zjuwangrui/25GAuto-Circuit-Modelling/resources/3.AD9910模块-SINC波点频输出代码/AD9910-STM32-DDS驱动板-V0.6/HARDWARE/ad9910/AD9910V1.C

/**********************************************************
                       康威电子

功能：stm32f103rct6控制
接口：按键接口请参照AD9910.H
时间：
版本：0.6
作者：康威电子
其他：

更多电子需求，请到淘宝店，康威电子竭诚为您服务 ^_^
https://kvdz.taobao.com/
**********************************************************/

#include "stm32f10x.h"
#include "AD9910.h"
#include "delay.h"
#include "sys.h"


/////三角波 波形数据，1024个点，14DAC值，最大16383
const u32 RAM_TRIG_WAVE[]=																																														
{
0,31,63,95,127,159,191,223,255,287,319,351,383,415,447,479,511,543,575,607,639,671,703,735,767,799,831,863,895,927,959,991,1023,1055,1087,1119,1151,1183,1215,1247,1279,1311,1343,1375,1407,1439,1471,1503,1535,1567,1599,1631,1663,1695,1727,1759,1791,1823,1855,1887,1919,1951,1983,2015,2047,2079,2111,2143,2175,2207,2239,2271,2303,2335,2367,2399,2431,2463,2495,2527,2559,2591,2623,2655,2687,2719,2751,2783,2815,2847,2879,2911,2943,2975,3007,3039,3071,3103,3135,3167,3199,3231,3263,3295,3327,3359,3391,3423,3455,3487,3519,3551,3583,3615,3647,3679,3711,3743,3775,3807,3839,3871,3903,3935,3967,3999,4031,4063,4095,4127,4159,4191,4223,4255,4287,4319,4351,4383,4415,4447,4479,4511,4543,4575,4607,4639,4671,4703,4735,4767,4799,4831,4863,4895,4927,4959,4991,5023,5055,5087,5119,5151,5183,5215,5247,5279,5311,5343,5375,5407,5439,5471,5503,5535,5567,5599,5631,5663,5695,5727,5759,5791,5823,5855,5887,5919,5951,5983,6015,6047,6079,6111,6143,6175,6207,6239,6271,6303,6335,6367,6399,6431,6463,6495,6527,6559,6591,6623,6655,6687,6719,6751,6783,6815,6847,6879,6911,6943,6975,7007,7039,7071,7103,7135,7167,7199,7231,7263,7295,7327,7359,7391,7423,7455,7487,7519,7551,7583,7615,7647,7679,7711,7743,7775,7807,7839,7871,7903,7935,7967,7999,8031,8063,8095,8127,8159,8191,8223,8255,8287,8319,8351,8383,8415,8447,8479,8511,8543,8575,8607,8639,8671,8703,8735,8767,8799,8831,8863,8895,8927,8959,8991,9023,9055,9087,9119,9151,9183,9215,9247,9279,9311,9343,9375,9407,9439,9471,9503,9535,9567,9599,9631,9663,9695,9727,9759,9791,98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
};


/////方波 波形数据，1024个点，14DAC值，最大16383
const u32 RAM_SQUARE_WAVE[]=																																														
{
0,0,0,0,0,0,0,0,0,0,0,0,0,0,0,0,0,0,0,0,0,0,0,0,0,0,0,0,0,0,0,0,0,0,0,0,0,0,0,0,0,0,0,0,0,0,0,0,0,0,0,0,0,0,0,0,0,0,0,0,0,0,0,0,0,0,0,0,0,0,0,0,0,0,0,0,0,0,0,0,0,0,0,0,0,0,0,0,0,0,0,0,0,0,0,0,0,0,0,0,0,0,0,0,0,0,0,0,0,0,0,0,0,0,0,0,0,0,0,0,0,0,0,0,0,0,0,0,0,0,0,0,0,0,0,0,0,0,0,0,0,0,0,0,0,0,0,0,0,0,0,0,0,0,0,0,0,0,0,0,0,0,0,0,0,0,0,0,0,0,0,0,0,0,0,0,0,0,0,0,0,0,0,0,0,0,0,0,0,0,0,0,0,0,0,0,0,0,0,0,0,0,0,0,0,0,0,0,0,0,0,0,0,0,0,0,0,0,0,0,0,0,0,0,0,0,0,0,0,0,0,0,0,0,0,0,0,0,0,0,0,0,0,0,0,0,0,0,0,0,0,0,0,0,0,0,0,0,0,0,0,0,0,0,0,0,0,0,0,0,0,0,0,0,0,0,0,0,0,0,0,0,0,0,0,0,0,0,0,0,0,0,0,0,0,0,0,0,0,0,0,0,0,0,0,0,0,0,0,0,0,0,0,0,0,0,0,0,0,0,0,0,0,0,0,0,0,0,0,0,0,0,0,0,0,0,0,0,0,0,0,0,0,0,0,0,0,0,0,0,0,0,0,0,0,0,0,0,0,0,0,0,0,0,0,0,0,0,0,0,0,0,0,0,0,0,0,0,0,0,0,0,0,0,0,0,0,0,0,0,0,0,0,0,0,0,0,0,0,0,0,0,0,0,0,0,0,0,0,0,0,0,0,0,0,0,0,0,0,0,0,0,0,0,0,0,0,0,0,0,0,0,0,0,0,0,0,0,0,0,0,0,0,0,0,0,0,0,0,0,0,0,0,0,0,0,0,0,0,0,0,0,0,0,0,0,0,0,0,0,0,0,0,0,0,0,0,0,0,0,0,0,0,0,0,0,0,0,0,0,0,0,0,0,0,0,0,0,0,0,0,0,0,0,0,0,0,0,0,0,0,0,16383,16383,16383,16383,16383,16383,16383,16383,16383,16383,16383,16383,16383,16383,16383,16383,16383,16383,16383,16383,16383,16383,16383,16383,16383,16383,16383,16383,16383,16383,16383,16383,16383,16383,16383,16383,16383,16383,16383,16383,16383,16383,16383,16383,16383,16383,16383,16383,16383,16383,16383,16383,16383,16383,16383,16383,16383,16383,16383,16383,16383,16383,16383,16383,16383,16383,16383,16383,16383,16383,16383,16383,16383,16383,16383,16383,16383,16383,16383,16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
** 入口参数 ：无
** 出口参数 ：无
** 函数说明 ：无
**************************************************************/
void AD9110_IOInit(void)
{
    GPIO_InitTypeDef GPIO_InitStructure ;

    RCC_APB2PeriphClockCmd(RCC_APB2Periph_GPIOB | RCC_APB2Periph_GPIOA | RCC_APB2Periph_GPIOC, ENABLE);	 //使能PB,PE端口时钟

    GPIO_InitStructure.GPIO_Pin = GPIO_Pin_10;
    GPIO_InitStructure.GPIO_Speed = GPIO_Speed_50MHz ;
    GPIO_InitStructure.GPIO_Mode = GPIO_Mode_Out_PP ;
    GPIO_Init(GPIOB , &GPIO_InitStructure) ;

    GPIO_InitStructure.GPIO_Pin = GPIO_Pin_6 | GPIO_Pin_4 | GPIO_Pin_5 | GPIO_Pin_8 | GPIO_Pin_2;
    GPIO_Init(GPIOA , &GPIO_InitStructure) ;

    GPIO_InitStructure.GPIO_Pin = GPIO_Pin_All ^ (GPIO_Pin_14 | GPIO_Pin_15);
    GPIO_Init(GPIOC , &GPIO_InitStructure) ;
}

/************************************************************
** 函数名称 ：void txd_8bit(uchar txdat)
** 函数功能 ：AD9910串行口写入数据
** 入口参数 ：8位寄存器数据
** 出口参数 ：无
** 函数说明 ：无
**************************************************************/
void txd_8bit(uchar txdat)
{
    uchar i, sbt;
    sbt = 0x80;
    SCLK = 0;
    for (i = 0; i < 8; i++)
    {
        if ((txdat & sbt) == 0) AD9910_SDIO = 0;
        else AD9910_SDIO = 1;
        SCLK = 1;
        sbt = sbt >> 1;
        SCLK = 0;
    }
}

/************************************************************
** 函数名称 ：void Write_32bit(u32 dat)	
** 函数功能 ：AD9910串行口写入数据
** 入口参数 ：32位寄存器数据
** 出口参数 ：无
** 函数说明 ：无
**************************************************************/
void Write_32bit(u32 dat)																							
{
	u8 i ;
	u32 com;
	com = 0x80000000;
	SCLK = 0;
	
	for(i=0; i < 32; i++)
	{
		if( (dat & com) == 0) 
			AD9910_SDIO = 0;
		else 
			AD9910_SDIO = 1;
		
		SCLK = 1;
		com = com >> 1;
		SCLK = 0;
	}
}

/************************************************************
** 函数名称 ：void Init_ad9910(void))
** 函数功能 ：初始化AD9910的管脚和最简单的内部寄存器的配置，
** 入口参数 ：无
** 出口参数 ：无
** 函数说明 ：无
**************************************************************/
void Init_AD9910(void)
{
    uchar k, m;

    AD9110_IOInit();//IO初始化
    AD9910_PWR = 0;//软件拉低

    PROFILE2 = 0;
		PROFILE1 = 0;
		PROFILE0 = 0;
    DRCTL = 0;
    DRHOLD = 0;
    MAS_REST = 1;
    delay_ms(5);
    MAS_REST = 0;

    CS = 0;
    txd_8bit(0x00);    //发送CFR1控制字地址
    for (m = 0; m < 4; m++)
        txd_8bit(cfr1[m]);
    CS = 1;
    for (k = 0; k < 10; k++);

    CS = 0;
    txd_8bit(0x01);    //发送CFR2控制字地址
    for (m = 0; m < 4; m++)
        txd_8bit(cfr2[m]);
    CS = 1;
    for (k = 0; k < 10; k++);

    CS = 0;
    txd_8bit(0x02);    //发送CFR3控制字地址
    for (m = 0; m < 4; m++)
        txd_8bit(cfr3[m]);
    CS = 1;
    for (k = 0; k < 10; k++);

    UP_DAT = 1;
    for(k = 0; k < 10; k++);
    UP_DAT = 0;
    delay_ms(1);

}

/************************************************************
** 函数名称 ：void Txfrc(void))
** 函数功能 ：向AD9910芯片发送频率，幅度等相关控制数据
** 入口参数 ：无
** 出口参数 ：无
** 函数说明 ：无
**************************************************************/
void Txfrc(void)
{
    uchar m;

    CS = 0;
    txd_8bit(0x0e);    //发送profile1控制字地址
    for (m = 0; m < 8; m++)
        txd_8bit(profile11[m]);
    CS = 1;

    UP_DAT = 1;
    UP_DAT = 0;
}

/************************************************************
** 函数名称 ：void AD9910_FreWrite(void))
** 函数功能 ：将需要的频率转换为对应的控制数据，保存进profile11并发送到芯片
** 入口参数 ：目标频率，单位Hz，范围0~420000000
** 出口参数 ：无
** 函数说明 ：无
**************************************************************/
void AD9910_FreWrite(ulong Freq)
{
    ulong Temp;
    Temp = (ulong)Freq * 4.294967296;	 //将输入频率因子分为四个字节  主频1GHz，32位相位累加器，故每Hz在的控制字增量 delta =  4.294967296 = (2^32)/1000000000
    profile11[7] = (uchar)Temp;
    profile11[6] = (uchar)(Temp >> 8);
    profile11[5] = (uchar)(Temp >> 16);
    profile11[4] = (uchar)(Temp >> 24);
    Txfrc();
}

/************************************************************
** 函数名称 ：void AD9910_AmpWrite(void))
** 函数功能 ：将幅度控制数据保存到profile11并写入芯片
** 入口参数 ：幅度控制字，范围0~16383
** 出口参数 ：无
** 函数说明 ：14位幅度控制字，控制数据0~16383对应输出幅度0~800mV左右
**************************************************************/
void AD9910_AmpWrite(uint16_t Amp)
{
    profile11[0] = (Amp % 16384) >> 8;
    profile11[1] = (Amp % 16384) & 0xff;
    Txfrc();
}

/************************************************************
** 函数名称 ：AD9910_RAM_WAVE_Set(AD9910_WAVE_ENUM wave)
** 函数功能 ：设置AD9910,RAM功能，向AD9910芯片内部RAM写入1024个点的波形数据，使模块可输出任意波形
							目前仅定义了三角波，方波，SINC波，三种波形数组
							用户也可自定义数组数据，使波形输出自己定义的任意波形(1024个数据，每个数据范围：0~16383)
** 入口参数 ：wave： TRIG_WAVE：三角波，SQUARE_WAVE：方波，SINC_WAVE：SINC波
** 出口参数 ：无
** 函数说明 ：RAM播放速率决定了输出波形的频率，输出频率与播放速率控制字参考以下说明
**************************************************************/
void AD9910_RAM_WAVE_Set(AD9910_WAVE_ENUM wave)
{
    int i;
    const u32 *srcWaveDta;
    u8 CFR1[] = {0x40, 0x40, 0x00, 0x00};																	// RAM回放目的：幅度;;开启AD9910反Sinc滤波

    //RAM_Profile0[1](高8位)  与  RAM_Profile0[2](低8位)共16位控制字M，决定了输出波形频率， 频率 = Fsysclk / (4*M) / 输出点数 = 1000000000 / (4*M) / 1024
		  u8 RAM_Profile0[] = {0x00, 0x00, 0x01, 0xff, 0xc0, 0x00, 0x00, 0x04};	//	地址步进率0X0001=    1,,从地址0回放到1023,共1024点，输出频率 = 1G / (4* 1) / 1024 = 244K Hz  // 连续循环模式RAM_PROx[7]=0x04
//    u8 RAM_Profile0[] = {0x00, 0x00, 0x0A, 0xff, 0xc0, 0x00, 0x00, 0x04};	//	地址步进率0X000A=   10,,从地址0回放到1023,共1024点，输出频率 = 1G / (4*10) / 1024 =  24K Hz  // 连续循环模式RAM_PROx[7]=0x04
//		u8 RAM_Profile0[] = {0x00, 0xFF, 0xFF, 0xff, 0xc0, 0x00, 0x00, 0x04};	//	地址步进率0XFFFF=65535,,从地址0回放到1023,共1024点，输出频率 = 1G / (4*65535) /1024 =3.7 Hz  // 连续循环模式RAM_PROx[7]=0x04
    CS = 0;
    txd_8bit(0x00);	// 将CFR1写入其寄存器0x00
    for(i = 0; i < 4; i++)
        txd_8bit(CFR1[i]);
    CS = 1;


    CS = 0;
    txd_8bit(0X0E);					//写寄存器RAM_Profile0
    for(i = 0; i < 8; i++)
    {
        txd_8bit(RAM_Profile0[i]);// 将RAM的起始和终止地址、地址步进率写入相应的寄存器  0x0e
    }
    CS = 1;

    UP_DAT = 0;// 更新AD9910
    UP_DAT = 1;
    UP_DAT = 0;

    CS = 0;
    txd_8bit(0x16);

    switch((uint8_t)wave)		//将数据定位到wave控制的数据数组
    {
			case TRIG_WAVE:			srcWaveDta = RAM_TRIG_WAVE;        break;
			case SQUARE_WAVE:		srcWaveDta = RAM_SQUARE_WAVE;      break;
			case SINC_WAVE:			srcWaveDta = RAM_SINC_WAVE;        break;
			default:						srcWaveDta = RAM_TRIG_WAVE;        break;
    }
    for(i = 0; i < 1024; i++)
    {
        Write_32bit(srcWaveDta[i] << 18);//将三角波(或其他任意波形)的数据数组写入ram,32位寄存器，14位DAC值，数据左对齐，故左移18位
    }

    CS = 1;
    CS = 0;
    txd_8bit(0x00);																																// 将CFR1写入其地址0x00
    CFR1[0] |= 0X80; //使能RAM
    for(i = 0; i < 4; i++)
        txd_8bit(CFR1[i]);
    CS = 1;

    UP_DAT = 0;// 更新AD9910
    UP_DAT = 1;
    UP_DAT = 0;
}
