zjuwangrui/25GAuto-Circuit-Modelling/resources/3.AD9910模块-SINC波点频输出代码/AD9910-STM32-DDS驱动板-V0.6/HARDWARE/ad9910/AD9910.H

#ifndef __AD9910_H__
#define __AD9910_H__

#include "stm32f10x.h"




#define uchar unsigned char
#define uint  unsigned int	
#define ulong  unsigned long int

#define AD9910_PWR		PCout(13)
#define AD9910_SDIO		PAout(5)
#define DRHOLD				PCout(1)
#define DROVER				PCout(2)
#define UP_DAT				PCout(3)
#define PROFILE1			PCout(10)
#define MAS_REST			PAout(6)
#define SCLK					PAout(2)
#define DRCTL					PAout(4)
#define OSK						PCout(8)
#define PROFILE0			PCout(4)
#define PROFILE2			PCout(5)
#define CS						PBout(10)


////#define AD9910_CSN_Set CS = 1
////#define AD9910_CSN_Clr CS = 0

////#define AD9910_IUP_Set UP_DAT = 1     
////#define AD9910_IUP_Clr UP_DAT = 0

typedef enum {
	TRIG_WAVE = 0,
	SQUARE_WAVE,
	SINC_WAVE,
} AD9910_WAVE_ENUM;

void AD9110_IOInit(void);
void Init_AD9910(void);
void AD9910_FreWrite(ulong Freq);										//дƵ��
void AD9910_AmpWrite(uint16_t Amp);


void AD9910_RAM_WAVE_Set(AD9910_WAVE_ENUM wave);



#endif
