zjuwangrui/25GAuto-Circuit-Modelling/resources/（全国一等奖）ZJA506-信电15组-G题-报告及资料/国赛/STM源代码及串口屏文件/Hardware/AD.h

#ifndef __AD_H
#define __AD_H

#include "stm32f10x.h"
#include "stdint.h"

#define NPT 1024



void AD_Init(void);
void AD3_Init(void);
void TIM8_init(uint16_t arr,uint16_t psc);
void ADC_DMA_Init(void);
void SwitchChannel(uint8_t channel);
void AD_SwitchToEXTI(void);
void AD_SwitchToTIM(void) ;
extern uint8_t adc_flag; 
extern uint8_t adc3_flag;
extern uint16_t AD_Value_buf[NPT];
extern uint16_t AD3_Value_buf[NPT];
#endif
