zjuwangrui/25GAuto-Circuit-Modelling/resources/（全国一等奖）ZJA506-信电15组-G题-报告及资料/国赛/STM源代码及串口屏文件/Hardware/Key.c

#include "stm32f10x.h"
#include "Delay.h"

void Key_Init(void)
{
    RCC_APB2PeriphClockCmd(RCC_APB2Periph_GPIOC,ENABLE);
    RCC_APB2PeriphClockCmd(RCC_APB2Periph_GPIOA,ENABLE);
    GPIO_InitTypeDef GPIO_InitStruct;
    // 初始化key2
	GPIO_InitStruct.GPIO_Mode = GPIO_Mode_IPU;
	GPIO_InitStruct.GPIO_Pin = GPIO_Pin_13;
	GPIO_InitStruct.GPIO_Speed = GPIO_Speed_50MHz;
	GPIO_Init(GPIOC, &GPIO_InitStruct);	
    // 初始化key1
    GPIO_InitStruct.GPIO_Mode = GPIO_Mode_IPU;
	GPIO_InitStruct.GPIO_Pin = GPIO_Pin_0;
	GPIO_InitStruct.GPIO_Speed = GPIO_Speed_50MHz;
	GPIO_Init(GPIOA, &GPIO_InitStruct);	
}
uint8_t Key_GetNum(void)
{
	uint8_t KeyNum = 0;		//定义变量，默认键码值为0
	
	if (GPIO_ReadInputDataBit(GPIOA, GPIO_Pin_0) == 1)			
	{
        
		Delay_us(20);											//延时消抖
		while (GPIO_ReadInputDataBit(GPIOA, GPIO_Pin_0) == 1);	//等待按键松手
		Delay_us(20);											//延时消抖
		KeyNum = 1;												//置键码为1
	}
	
	if (GPIO_ReadInputDataBit(GPIOC, GPIO_Pin_13) == 1)			
	{
		Delay_us(20);											//延时消抖
		while (GPIO_ReadInputDataBit(GPIOC, GPIO_Pin_13) == 1);	//等待按键松手
		Delay_us(20);											//延时消抖
		KeyNum = 2;												//置键码为2
	}
	
	return KeyNum;			//返回键码值，如果没有按键按下，所有if都不成立，则键码为默认值0
}
