zjuwangrui/25GAuto-Circuit-Modelling/resources/（全国一等奖）ZJA506-信电15组-G题-报告及资料/国赛/STM源代码及串口屏文件/Hardware/Serial.h

#ifndef __SERIAL_H
#define __SERIAL_H

#include <stdio.h>
#include "stm32f10x.h"                  // Device header

void Serial_Init(void);
void Serial_SendByte(uint8_t Byte);
void Serial_SendArray(uint8_t *Array, uint16_t Length);
void Serial_SendString(char *String);
void Serial_SendNumber(uint32_t Number, uint8_t Length);
void Serial_Printf(char *format, ...);

uint8_t Serial_GetRxFlag(void);
uint8_t Serial_GetRxData(void);

#endif
