zjuwangrui/25GAuto-Circuit-Modelling/resources/（全国一等奖）ZJA506-信电15组-G题-报告及资料/国赛/STM源代码及串口屏文件/System/timer.c

#include "timer.h" 
#include "DAC902.h"





extern void Triangle_Wave(void);

void TIM4_Int_Init(u16 arr,u16 psc)
{
    TIM_TimeBaseInitTypeDef  TIM_TimeBaseStructure;
	NVIC_InitTypeDef NVIC_InitStructure;

	RCC_APB1PeriphClockCmd(RCC_APB1Periph_TIM4, ENABLE);
	

	TIM_TimeBaseStructure.TIM_Period = arr;
	TIM_TimeBaseStructure.TIM_Prescaler =psc;
	TIM_TimeBaseStructure.TIM_ClockDivision = TIM_CKD_DIV1;
	TIM_TimeBaseStructure.TIM_CounterMode = TIM_CounterMode_Up;
	TIM_TimeBaseInit(TIM4, &TIM_TimeBaseStructure);
 
	TIM_ITConfig(TIM4,TIM_IT_Update,ENABLE );


	NVIC_InitStructure.NVIC_IRQChannel = TIM4_IRQn;
	NVIC_InitStructure.NVIC_IRQChannelPreemptionPriority = 0;
	NVIC_InitStructure.NVIC_IRQChannelSubPriority = 0;
	NVIC_InitStructure.NVIC_IRQChannelCmd = ENABLE;
	NVIC_Init(&NVIC_InitStructure);


	TIM_Cmd(TIM4, ENABLE);
}



void TIM4_IRQHandler(void)
{
	if (TIM_GetITStatus(TIM4, TIM_IT_Update) != RESET)
		{
		TIM_ClearITPendingBit(TIM4, TIM_IT_Update  );
			Sine_Wave(); 
		}
}
